barry-ha/Griduino/docs/img/NMEATime2-screenshot.PNG

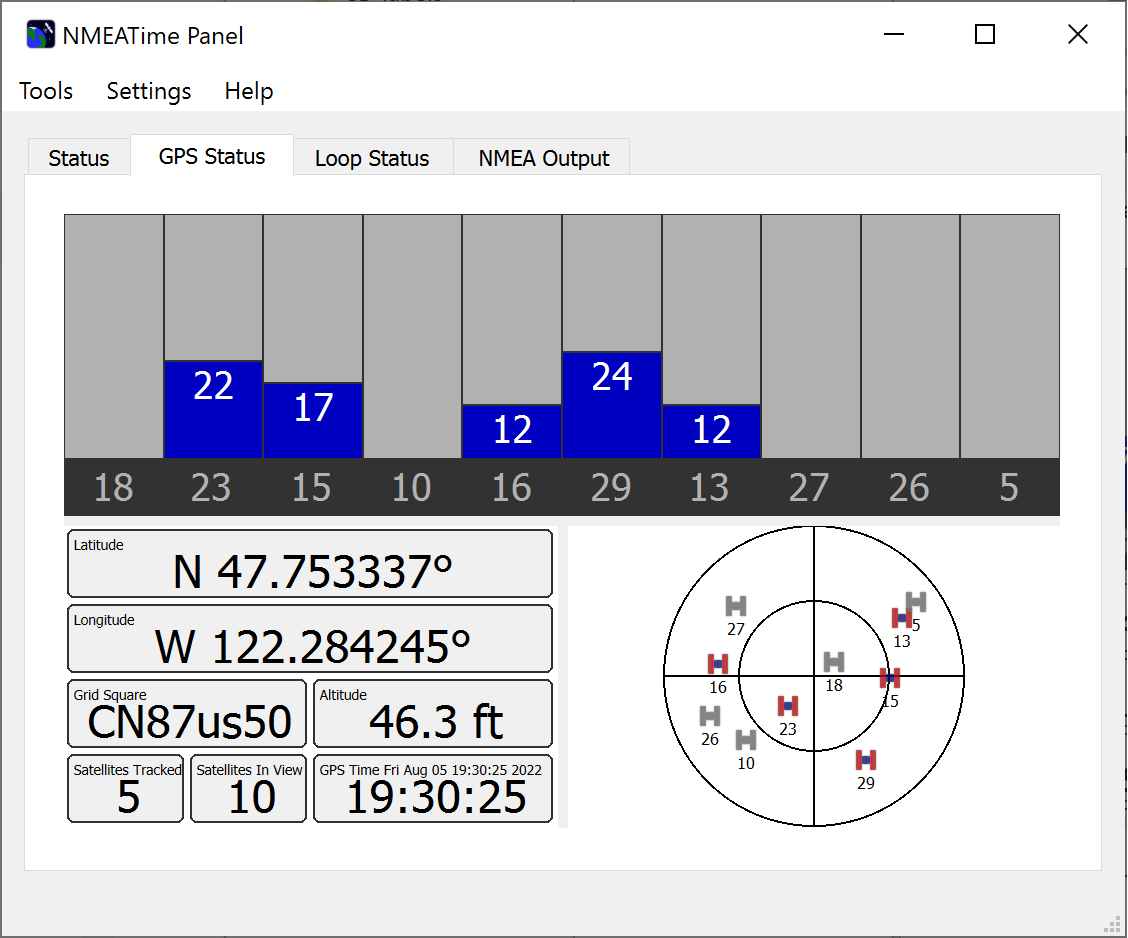
docs/img/NMEATime2-screenshot.PNG
