barry-ha/Griduino/downloads/img/compass-img6840.jpg

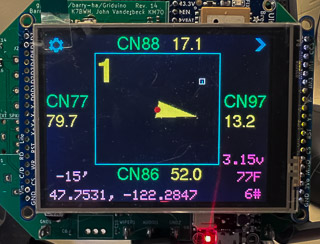
downloads/img/compass-img6840.jpg
