barry-ha/Griduino/examples/Altimeter/2020-03-06 Griduino Altimeter img6224.jpg

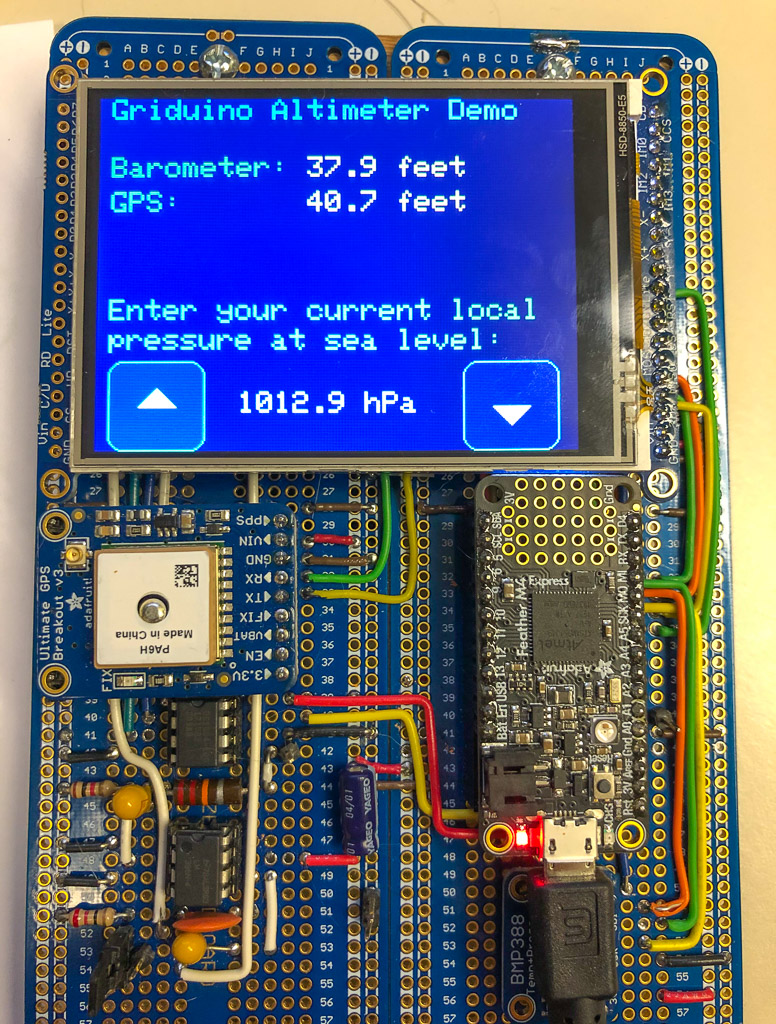
examples/Altimeter/2020-03-06 Griduino Altimeter img6224.jpg
