barry-ha/Griduino/examples/Altimeter/2021-01-30 Griduino-altimeter-img03912.jpg

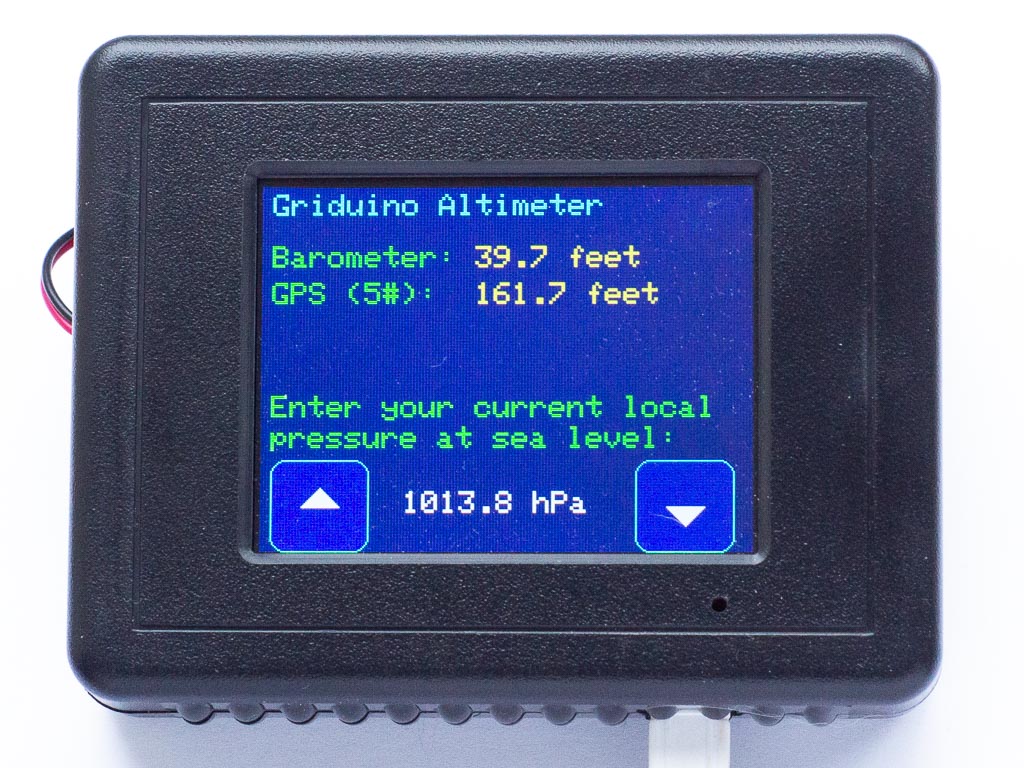
examples/Altimeter/2021-01-30 Griduino-altimeter-img03912.jpg
