barry-ha/Griduino/examples/Baroduino/2020_09_30_Baroduino_img7400.jpg

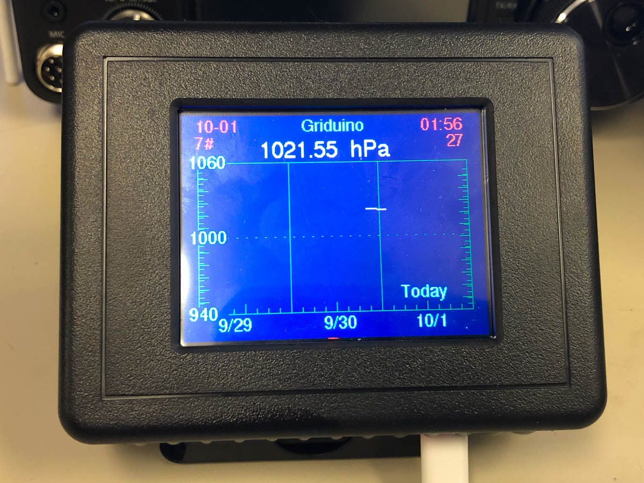
examples/Baroduino/2020_09_30_Baroduino_img7400.jpg
