barry-ha/Griduino/examples/Barograph/2020-01-17 Barograph John KM7O img1087.JPG

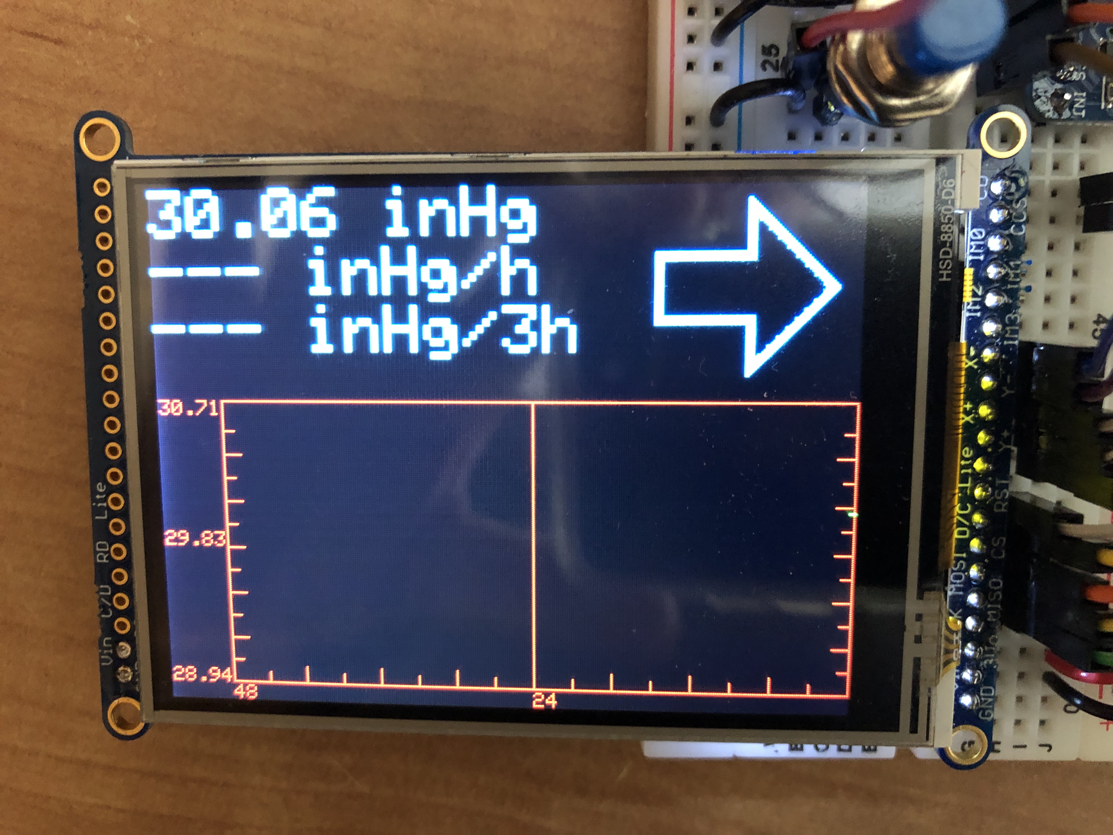
examples/Barograph/2020-01-17 Barograph John KM7O img1087.JPG
