barry-ha/Griduino/examples/Flash_file_directory_list/2021-04-06 file system img8184.jpg

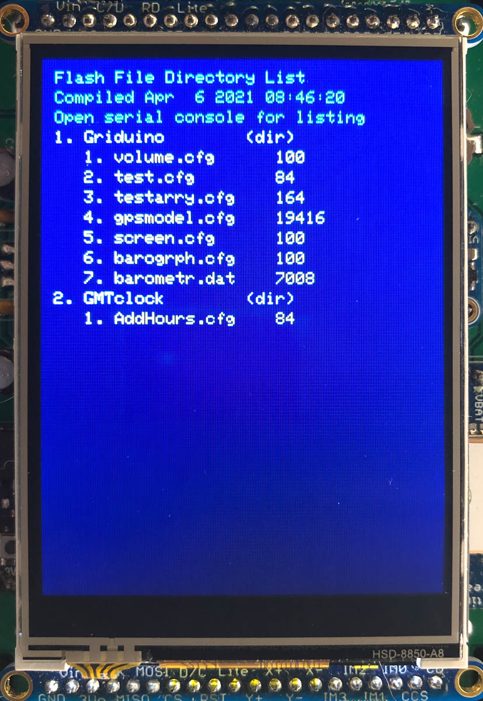
examples/Flash_file_directory_list/2021-04-06 file system img8184.jpg
