barry-ha/Griduino/examples/Barograph/2020-03-14 Barograph Barry K7BWH img6243.jpg

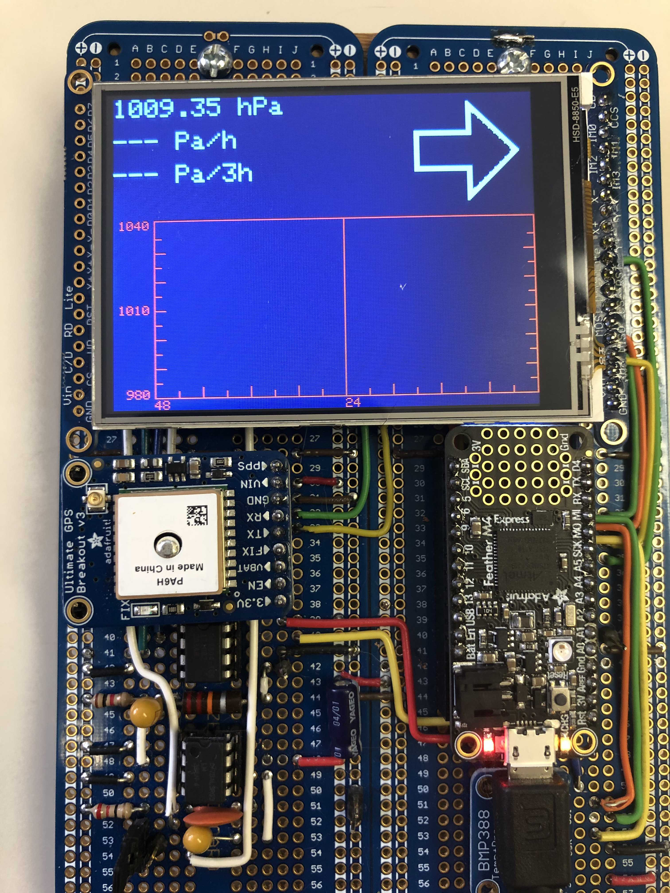
examples/Barograph/2020-03-14 Barograph Barry K7BWH img6243.jpg
